kovarmi9/BachelorThesis-Astrochronograph/src/LaTex/images/komponenty/GNSS.png

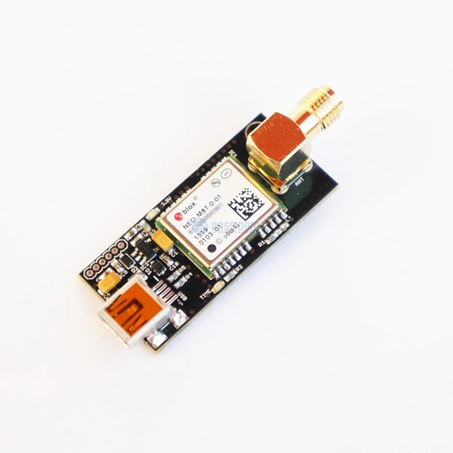
src/LaTex/images/komponenty/GNSS.png
