kovarmi9/BachelorThesis-Astrochronograph/src/LaTex/images/schema_DCF77_signalu.png

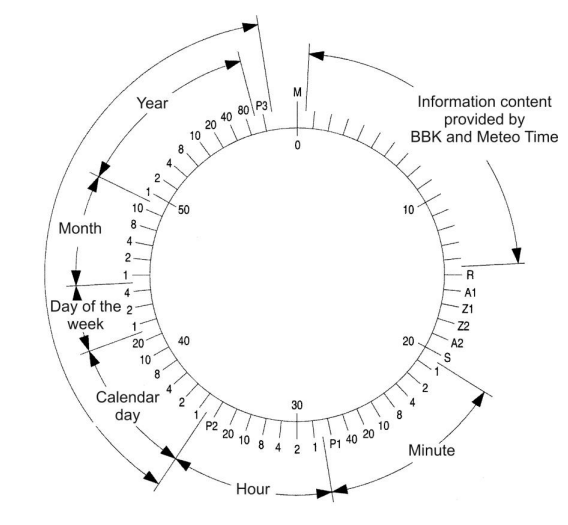
src/LaTex/images/schema_DCF77_signalu.png
