kovarmi9/BachelorThesis-Astrochronograph/src/Arduino/Components/TS_Reader/TS_Reader.ino

#include "TS_Reader.h"

void setup() {
  Stroj.begin(9600);
  Serial.begin(9600);
}

void loop() {
  // posílání GET/M/WI21 do počítače každou vteřinu
  Stroj.println("GET/M/WI21");

  // čtení dat
  if (Stroj.available()) {
    String SerialData = Stroj.readStringUntil('\n');

    // vypisování dat na sériový monitor
    if (SerialData != "") {
      Serial.println(SerialData);
    }
  }

  delay(500);
}
