kovarmi9/BachelorThesis-Astrochronograph/src/Arduino/Components/TS_Reader/TS_Reader.h

#ifndef TS_READER_H
#define TS_READER_H

#include <Arduino.h>
#include <SoftwareSerial.h>

// nastavení propojovacích pinů
#define RX 9
#define TX 10

// deklarace objektu SoftwareSerial
extern SoftwareSerial Stroj;

#endif // TS_READER_H
